WiseLord/ampcontrol-f103/src/tuner/tuner.c

#include "tuner.h"

#include <string.h>

#include "rds/parser.h"
#include "settings.h"
#include "stations.h"

#ifdef _RDA580X
#include "rda580x.h"
#endif
#ifdef _SI470X
#include "si470x.h"
#endif
#ifdef _TEA5767
#include "tea5767.h"
#endif
#ifdef _LC7213X
#include "lc7213x.h"
#endif

static Tuner tuner;

void tunerTestInit(TunerParam *tPar, TunerStatus *status)
{
    switch (tPar->band) {
    case TUNER_BAND_FM_JAPAN:
        tPar->fMin = 7600;
        tPar->fMax = 9100;
        break;
    case TUNER_BAND_FM_WORLDWIDE:
        tPar->fMin = 7600;
        tPar->fMax = 10800;
        break;
    case TUNER_BAND_FM_EASTEUROPE:
        tPar->fMin = 6500;
        tPar->fMax = 7600;
        break;
    default:
        tPar->fMin = 8700;
        tPar->fMax = 10800;
        break;
    }

    switch (tPar->step) {
    case TUNER_STEP_50K:
        tPar->fStep = 5;
        break;
    case TUNER_STEP_200K:
        tPar->fStep = 20;
        break;
    default:
        tPar->fStep = 10;
        break;
    }

    status->rssi = 10;
    status->flags = TUNER_STATUS_STEREO;
}

void tunerTestSetFreq(uint16_t value)
{
    tuner.status.freq = value;
}

static const TunerApi tunerTestApi = {
    .init = tunerTestInit,
    .setFreq = tunerTestSetFreq,
    .seek = tunerStep,
};


void tunerReadSettings(TunerIC defIC)
{
    stationsInit();

    // Read stored parameters
    memset(&tuner, 0, sizeof(tuner));

    tuner.par.ic = settingsRead(PARAM_TUNER_IC, defIC);
    tuner.par.band = settingsRead(PARAM_TUNER_BAND, TUNER_BAND_FM_US_EUROPE);
    tuner.par.step = settingsRead(PARAM_TUNER_STEP, TUNER_STEP_100K);
    tuner.par.deemph = settingsRead(PARAM_TUNER_DEEMPH, TUNER_DEEMPH_50u);

    tuner.par.volume = settingsRead(PARAM_TUNER_VOLUME, TUNER_VOLUME_MAX);
    tuner.status.freq = settingsRead(PARAM_TUNER_FREQ, 9950);
    tuner.par.flags = settingsRead(PARAM_TUNER_FLAGS, TUNER_PARAM_RDS);

    stationFavInit();

    // API initialization
    switch (tuner.par.ic) {
#ifdef _RDA580X
    case TUNER_IC_RDA5807:
        tuner.api = rda580xGetApi();
        break;
#endif
#ifdef _SI470X
    case TUNER_IC_SI4703:
        tuner.api = si470xGetApi();
        break;
#endif
#ifdef _TEA5767
    case TUNER_IC_TEA5767:
        tuner.api = tea5767GetApi();
        break;
#endif
#ifdef _LC7213X
    case TUNER_IC_LC7213X:
        tuner.api = lc7213xGetApi();
        break;
#endif
    case TUNER_IC_TEST:
        tuner.api = &tunerTestApi;
        break;
    default:
        tuner.api = NULL;
        break;
    }
}

void tunerSaveSettings(void)
{
    settingsStore(PARAM_TUNER_FREQ, (int16_t)tuner.status.freq);
    settingsStore(PARAM_TUNER_FLAGS, tuner.par.flags & ~TUNER_PARAM_MUTE);
}

void tunerInit(void)
{
    rdsParserReset();

    if (tuner.api && tuner.api->init) {
        tuner.api->init(&tuner.par, &tuner.status);
    }
}

Tuner *tunerGet(void)
{
    return &tuner;
}

void tunerSetPower(bool value)
{
    rdsParserReset();

    if (!value) {
        tunerSaveSettings();
    }

    if (tuner.api && tuner.api->setPower) {
        tuner.api->setPower(value);
    }
}

void tunerSetFreq(uint16_t value)
{
    rdsParserReset();

    const uint16_t freqMin = tuner.par.fMin;
    const uint16_t freqMax = tuner.par.fMax;

    if (value < freqMin) {
        value = freqMin;
    } else if (value > freqMax) {
        value = freqMax;
    }

    if (tuner.api && tuner.api->setFreq) {
        tuner.status.freq = value;
        tuner.api->setFreq(value);
    }
}

void tunerSetMute(bool value)
{
    if (value) {
        tuner.par.flags |= TUNER_PARAM_MUTE;
    } else {
        tuner.par.flags &= ~TUNER_PARAM_MUTE;
    }

    if (tuner.api && tuner.api->setMute) {
        tuner.api->setMute(value);
    }
}

void tunerSetBassBoost(bool value)
{
    if (value) {
        tuner.par.flags |= TUNER_PARAM_BASS;
    } else {
        tuner.par.flags &= ~TUNER_PARAM_BASS;
    }

    if (tuner.api && tuner.api->setBassBoost) {
        tuner.api->setBassBoost(value);
    }
}

void tunerSetForcedMono(bool value)
{
    if (value) {
        tuner.par.flags |= TUNER_PARAM_MONO;
    } else {
        tuner.par.flags &= ~TUNER_PARAM_MONO;
    }

    if (tuner.api && tuner.api->setForcedMono) {
        tuner.api->setForcedMono(value);
    }
}

void tunerSetRds(bool value)
{
    rdsParserReset();

    if (value) {
        tuner.par.flags |= TUNER_PARAM_RDS;
    } else {
        tuner.par.flags &= ~TUNER_PARAM_RDS;
    }

    if (tuner.api && tuner.api->setRds) {
        tuner.api->setRds(value);
    }
}

void tunerSetVolume(int8_t value)
{
    tuner.par.volume = value;

    if (tuner.api && tuner.api->setVolume) {
        tuner.api->setVolume(value);
    }
}

void tunerSeek(int8_t direction)
{
    rdsParserReset();

    if (tuner.api && tuner.api->seek) {
        tuner.api->seek(direction);
    }
}

void tunerStep(int8_t direction)
{
    uint16_t freq = tuner.status.freq;
    const uint16_t fMin = tuner.par.fMin;
    const uint16_t fMax = tuner.par.fMax;

    if (direction > 0) {
        if (freq == fMax) {
            freq = fMin;
        } else {
            freq += tuner.par.fStep;
        }
    } else {
        if (freq == fMin) {
            freq = fMax;
        } else {
            freq -= tuner.par.fStep;
        }
    }

    tunerSetFreq(freq);
}

void tunerMove(int8_t direction)
{
    if (tuner.par.flags & TUNER_PARAM_STA_MODE) {
        if (stationGetCount() > 0) {
            stationSeek(direction);
        } else {
            tunerStep(direction);
        }
    } else {
        tunerStep(direction);
    }
}

void tunerUpdateStatus(void)
{
    tuner.status.flags = TUNER_STATUS_INIT;

    if (tuner.api && tuner.api->updateStatus) {
        tuner.api->updateStatus();
    }
}
