WiseLord/ampcontrol-f103/src/tr/labels_en.c

#include "labels.h"

const char *const labels_en[LABEL_END] = {
    [LABEL_SUNDAY]          = "SUNDAY",
    [LABEL_MONDAY]          = "MONDAY",
    [LABEL_TUESDAY]         = "TUESDAY",
    [LABEL_WEDNESDAY]       = "WEDNESDAY",
    [LABEL_THURSDAY]        = "THURSDAY",
    [LABEL_FRIDAY]          = "FRIDAY",
    [LABEL_SATURDAY]        = "SATURDAY",

    [LABEL_VOLUME]          = "Volume",
    [LABEL_BASS]            = "Bass",
    [LABEL_MIDDLE]          = "Middle",
    [LABEL_TREBLE]          = "Treble",
    [LABEL_BALANCE]         = "Balance",
    [LABEL_FRONTREAR]       = "Front/rear",
    [LABEL_CENTER]          = "Center",
    [LABEL_SUBWOOFER]       = "Subwoofer",
    [LABEL_PREAMP]          = "Preamp",
    [LABEL_LOUDNESS]        = "Loudness",

    [LABEL_BASS_FREQ]       = "Bass freq",
    [LABEL_BASS_QUAL]       = "Bass Q",
    [LABEL_MIDDLE_KFREQ]    = "Middle freq",
    [LABEL_MIDDLE_QUAL]     = "Middle Q",
    [LABEL_TREBLE_KFREQ]    = "Treble freq",
    [LABEL_SUB_CUT_FREQ]    = "Sub cut freq",
    [LABEL_LOUD_PEAK_FREQ]  = "Loudness freq",

    [LABEL_IN_TUNER]        = "Tuner",
    [LABEL_IN_PC]           = "Computer",
    [LABEL_IN_AUX]          = "AUX",
    [LABEL_IN_BLUETOOTH]    = "Bluetooth",
    [LABEL_IN_KARADIO]      = "KaRadio",
    [LABEL_IN_USB]          = "USB",
    [LABEL_IN_SDCARD]       = "SD card",
    [LABEL_IN_MPD]          = "MPD",

    [LABEL_BOOL_OFF]        = "OFF",
    [LABEL_BOOL_ON]         = "ON",

    [LABEL_DB]              = "dB",
    [LABEL_HZ]              = "Hz",
    [LABEL_K]               = "k",

    [LABEL_IN_WAIT]         = "Waiting for",

    [LABEL_TUNER_FM_STATION_NAME]   = "FM station name",

    FOREACH_TUNER_IC(GENERATE_TUNER_IC_TEXT)

    [LABEL_TUNER_BAND + TUNER_BAND_FM_US_EUROPE]    = "US/Europe FM",
    [LABEL_TUNER_BAND + TUNER_BAND_FM_JAPAN]        = "Japan FM",
    [LABEL_TUNER_BAND + TUNER_BAND_FM_WORLDWIDE]    = "Worldwide FM",
    [LABEL_TUNER_BAND + TUNER_BAND_FM_EASTEUROPE]   = "East Europe FM",

    [LABEL_TUNER_STEP + TUNER_STEP_50K]     = "50kHz",
    [LABEL_TUNER_STEP + TUNER_STEP_100K]    = "100kHz",
    [LABEL_TUNER_STEP + TUNER_STEP_200K]    = "200kHz",

    [LABEL_TUNER_DEEMPH + TUNER_DEEMPH_50u] = "50us",
    [LABEL_TUNER_DEEMPH + TUNER_DEEMPH_75u] = "75us",

    [LABEL_SPECTRUM_MODE + SP_MODE_STEREO]      = "Stereo",
    [LABEL_SPECTRUM_MODE + SP_MODE_MIRROR]      = "Mirror",
    [LABEL_SPECTRUM_MODE + SP_MODE_INVERTED]    = "Inverted",
    [LABEL_SPECTRUM_MODE + SP_MODE_ANTIMIRROR]  = "Antimirror",
    [LABEL_SPECTRUM_MODE + SP_MODE_MIXED]       = "Mixed",

    [LABEL_PAL_MODE + PAL_SNOW]         = "Snow",
    [LABEL_PAL_MODE + PAL_AQUA]         = "Aqua",
    [LABEL_PAL_MODE + PAL_FIRE]         = "Fire",

    FOREACH_AUDIO_IC(GENERATE_AUDIO_IC_TEXT)

    [LABEL_AUDIO_MODE + AUDIO_MODE_2_0]     = "2.0",
    [LABEL_AUDIO_MODE + AUDIO_MODE_2_1]     = "2.1",
    [LABEL_AUDIO_MODE + AUDIO_MODE_4_0]     = "4.0",
    [LABEL_AUDIO_MODE + AUDIO_MODE_4_1]     = "4.1",
    [LABEL_AUDIO_MODE + AUDIO_MODE_5_1]     = "5.1",

    [LABEL_ALARM_DAY + ALARM_DAY_OFF]       = "Disabled",
    [LABEL_ALARM_DAY + ALARM_DAY_WEEKDAYS]  = "Weekdays",
    [LABEL_ALARM_DAY + ALARM_DAY_ALL_DAYS]  = "All days",

    // NOTE: Keep in sync with MenuIdx in menu.h
    [LABEL_MENU + MENU_NULL]            = "Up menu",

    [LABEL_MENU + MENU_SETUP]           = "Settings",

    [LABEL_MENU + MENU_SETUP_SYSTEM]    = "System",
    [LABEL_MENU + MENU_SETUP_AUDIO]     = "Audio",
    [LABEL_MENU + MENU_SETUP_TUNER]     = "Tuner",
    [LABEL_MENU + MENU_SETUP_SPECTRUM]  = "Spectrum",
    [LABEL_MENU + MENU_SETUP_DISPLAY]   = "Display",
    [LABEL_MENU + MENU_SETUP_ALARM]     = "Alarm",
    [LABEL_MENU + MENU_SETUP_RC]        = "Remote",

    [LABEL_MENU + MENU_SYSTEM_LANG]     = "Language",
    [LABEL_MENU + MENU_SYSTEM_I2C_EXT]  = "I2C expander",
    [LABEL_MENU + MENU_SYSTEM_ENC_RES]  = "Encoder resolution",
    [LABEL_MENU + MENU_SYSTEM_SIL_TIM]  = "Silence timer",
    [LABEL_MENU + MENU_SYSTEM_RTC_CORR] = "Time correction",
    [LABEL_MENU + MENU_SYSTEM_STBY_LOW] = "STBY active 0",
    [LABEL_MENU + MENU_SYSTEM_MUTE_LOW] = "MUTE active 0",

    [LABEL_MENU + MENU_I2C_EXT_IN_STAT] = "Input status",
    [LABEL_MENU + MENU_I2C_EXT_GPIO]    = "GPIO control",

    [LABEL_MENU + MENU_AUDIO_IC]        = "Audioproc",
    [LABEL_MENU + MENU_AUDIO_SHOWDB]    = "Show in dB",
    [LABEL_MENU + MENU_AUDIO_MODE]      = "Audio mode",
    [LABEL_MENU + MENU_AUDIO_IN]        = "Input",

    [LABEL_MENU + MENU_TUNER_IC]        = "Tuner IC",
    [LABEL_MENU + MENU_TUNER_BAND]      = "Band",
    [LABEL_MENU + MENU_TUNER_STEP]      = "Scan step",
    [LABEL_MENU + MENU_TUNER_DEEMPH]    = "Deemphasys",
    [LABEL_MENU + MENU_TUNER_STA_MODE]  = "Stations mode",
    [LABEL_MENU + MENU_TUNER_FMONO]     = "Force mono",
    [LABEL_MENU + MENU_TUNER_RDS]       = "Enable RDS",
    [LABEL_MENU + MENU_TUNER_BASS]      = "Bass boost",
    [LABEL_MENU + MENU_TUNER_VOLUME]    = "Volume",

    [LABEL_MENU + MENU_ALARM_HOUR]      = "Hour",
    [LABEL_MENU + MENU_ALARM_MINUTE]    = "Minute",
    [LABEL_MENU + MENU_ALARM_DAYS]      = "Days",

    [LABEL_MENU + MENU_SPECTRUM_MODE]   = "Display mode",
    [LABEL_MENU + MENU_SPECTRUM_PEAKS]  = "Peak level",
    [LABEL_MENU + MENU_SPECTRUM_GRAD]   = "Gradient",

    [LABEL_MENU + MENU_DISPLAY_BR_STBY] = "STBY brightness",
    [LABEL_MENU + MENU_DISPLAY_BR_WORK] = "Brightness",
    [LABEL_MENU + MENU_DISPLAY_ROTATE]  = "Rotate",
    [LABEL_MENU + MENU_DISPLAY_DEF]     = "Main screen",
    [LABEL_MENU + MENU_DISPLAY_PALETTE] = "Palette",
    [LABEL_MENU + MENU_DISPLAY_SCRSAVER] = "Screensaver",

    // NOTE: Keep in sync with cmd.h define list
    [LABEL_MENU + MENU_RC_STBY_SWITCH]  = "Switch standby",
    [LABEL_MENU + MENU_RC_MUTE]         = "Mute",
    [LABEL_MENU + MENU_RC_VOL_UP]       = "Volume up",
    [LABEL_MENU + MENU_RC_VOL_DOWN]     = "Volume down",
    [LABEL_MENU + MENU_RC_MENU]         = "Menu",
    [LABEL_MENU + MENU_RC_CHAN_NEXT]    = "Next chan",
    [LABEL_MENU + MENU_RC_CHAN_PREV]    = "Prev chan",
    [LABEL_MENU + MENU_RC_DIG]          = "Digit",
    [LABEL_MENU + MENU_RC_IN_NEXT]      = "Next input",
    [LABEL_MENU + MENU_RC_NAV_OK]       = "OK",
    [LABEL_MENU + MENU_RC_NAV_BACK]     = "Back",
    [LABEL_MENU + MENU_RC_NAV_RIGHT]    = "Right",
    [LABEL_MENU + MENU_RC_NAV_UP]       = "Up",
    [LABEL_MENU + MENU_RC_NAV_LEFT]     = "Left",
    [LABEL_MENU + MENU_RC_NAV_DOWN]     = "Down",
    [LABEL_MENU + MENU_RC_BASS_UP]      = "Bass up",
    [LABEL_MENU + MENU_RC_BASS_DOWN]    = "Bass down",
    [LABEL_MENU + MENU_RC_MIDDLE_UP]    = "Middle up",
    [LABEL_MENU + MENU_RC_MIDDLE_DOWN]  = "Middle down",
    [LABEL_MENU + MENU_RC_TREBLE_UP]    = "Treble up",
    [LABEL_MENU + MENU_RC_TREBLE_DOWN]  = "Treble down",
    [LABEL_MENU + MENU_RC_LOUDNESS]     = "Loudness",
    [LABEL_MENU + MENU_RC_SURROUND]     = "Surround",
    [LABEL_MENU + MENU_RC_EFFECT_3D]    = "3D-effect",
    [LABEL_MENU + MENU_RC_TONE_BYPASS]  = "Bypass tone",
    [LABEL_MENU + MENU_RC_TIME]         = "Time",
    [LABEL_MENU + MENU_RC_STOP]         = "Stop",
    [LABEL_MENU + MENU_RC_PLAY_PAUSE]   = "Play/pause",
    [LABEL_MENU + MENU_RC_REW]          = "Rewind",
    [LABEL_MENU + MENU_RC_FWD]          = "Flash forward",
    [LABEL_MENU + MENU_RC_TIMER]        = "Timer",
    [LABEL_MENU + MENU_RC_SP_MODE]      = "Spectrum mode",
    [LABEL_MENU + MENU_RC_SCR_DEF]      = "Default screen",
    [LABEL_MENU + MENU_RC_BT_IN_NEXT]   = "Next BT input",
    [LABEL_MENU + MENU_RC_TUNER_MONO]   = "Tuner mono",
    [LABEL_MENU + MENU_RC_REPEAT]       = "Repeat",
    [LABEL_MENU + MENU_RC_RANDOM]       = "Random",
};
