WiseLord/ampcontrol-f103/src/tr/labels_tr.c

#include "labels.h"

const char *const labels_tr[LABEL_END] = {
    [LABEL_SUNDAY]          = "Pazar",
    [LABEL_MONDAY]          = "Pazartesi",
    [LABEL_TUESDAY]         = "Salı",
    [LABEL_WEDNESDAY]       = "Çarşamba",
    [LABEL_THURSDAY]        = "Perşembe",
    [LABEL_FRIDAY]          = "Cuma",
    [LABEL_SATURDAY]        = "Cumartesi",

    [LABEL_VOLUME]          = "Volum",
    [LABEL_BASS]            = "Bass",
    [LABEL_MIDDLE]          = "Orta Ses",
    [LABEL_TREBLE]          = "Tiz",
    [LABEL_BALANCE]         = "Sağ/Sol Denge",
    [LABEL_FRONTREAR]       = "Ön/Arka Denge",
    [LABEL_CENTER]          = "Merkez",
    [LABEL_SUBWOOFER]       = "Subwoofer",
    [LABEL_PREAMP]          = "Kazanç",

    [LABEL_IN_TUNER]        = "Radio",
    [LABEL_IN_PC]           = "Bilgisayar",
    //    [LABEL_IN_AUX]          = "AUX",
    //    [LABEL_IN_BLUETOOTH]    = "Bluetooth",
    //    [LABEL_IN_KARADIO]      = "KaRadio",
    //    [LABEL_IN_USB]          = "USB",
    [LABEL_IN_SDCARD]       = "SD Kart",
//    [LABEL_IN_MPD]          = "MPD",

    [LABEL_BOOL_OFF]        = "Kapalı",
    [LABEL_BOOL_ON]         = "Açık",

//    [LABEL_IN_WAIT]         = "Wait for",

    [LABEL_TUNER_FM_STATION_NAME]   = "FM Radyo İsimleri:",

    [LABEL_TUNER_IC + TUNER_IC_NO]      = "Yok",

    [LABEL_TUNER_BAND + TUNER_BAND_FM_US_EUROPE]    = "ABD/Avrupa FM",
    [LABEL_TUNER_BAND + TUNER_BAND_FM_JAPAN]        = "Japan FM",
    [LABEL_TUNER_BAND + TUNER_BAND_FM_WORLDWIDE]    = "Dünya Çapında FM",
    [LABEL_TUNER_BAND + TUNER_BAND_FM_EASTEUROPE]   = "Doğu Avrupa FM",

    [LABEL_TUNER_STEP + TUNER_STEP_50K]     = "50kHz",
    [LABEL_TUNER_STEP + TUNER_STEP_100K]    = "100kHz",
    [LABEL_TUNER_STEP + TUNER_STEP_200K]    = "200kHz",

    [LABEL_TUNER_DEEMPH + TUNER_DEEMPH_50u] = "50us",
    [LABEL_TUNER_DEEMPH + TUNER_DEEMPH_75u] = "75us",

    [LABEL_SPECTRUM_MODE + SP_MODE_STEREO]      = "Stereo",
//    [LABEL_SPECTRUM_MODE + SP_MODE_MIRROR]      = "Mirror",
//    [LABEL_SPECTRUM_MODE + SP_MODE_INVERTED]    = "Inverted",
//    [LABEL_SPECTRUM_MODE + SP_MODE_ANTIMIRROR]  = "Antimirror",
    [LABEL_SPECTRUM_MODE + SP_MODE_MIXED]       = "Karışık",

    [LABEL_PAL_MODE + PAL_SNOW]         = "Kar Teması",
    [LABEL_PAL_MODE + PAL_AQUA]         = "Su Teması",
    [LABEL_PAL_MODE + PAL_FIRE]         = "Ateş Teması",

    [LABEL_AUDIO_IC + AUDIO_IC_NO]      = "Yok",

    [LABEL_ALARM_DAY + ALARM_DAY_OFF]       = "Kapalı",
    [LABEL_ALARM_DAY + ALARM_DAY_WEEKDAYS]  = "Hafta İçi",
    [LABEL_ALARM_DAY + ALARM_DAY_ALL_DAYS]  = "Tüm Günler",

    // NOTE: Keep in sync with MenuIdx in menu.h
    [LABEL_MENU + MENU_NULL]            = "Bir Önceki Menü'ye Dön",

    [LABEL_MENU + MENU_SETUP]           = "Menü Ayarları",

    [LABEL_MENU + MENU_SETUP_SYSTEM]    = "Sistem Ayarı",
    [LABEL_MENU + MENU_SETUP_AUDIO]     = "Ses İşlemci Ayarı",
    [LABEL_MENU + MENU_SETUP_TUNER]     = "Radyo İşlemci Ayarı",
    [LABEL_MENU + MENU_SETUP_SPECTRUM]  = "Spectrum Ayarı",
    [LABEL_MENU + MENU_SETUP_DISPLAY]   = "Ekran Ayarı",
    [LABEL_MENU + MENU_SETUP_ALARM]     = "Alarm Ayarı",
    [LABEL_MENU + MENU_SETUP_RC]        = "Kumanda Ayarı",

    [LABEL_MENU + MENU_SYSTEM_LANG]     = "Dil Seçeneği",
    [LABEL_MENU + MENU_SYSTEM_I2C_EXT]  = "I2C Genişletici",
    [LABEL_MENU + MENU_SYSTEM_ENC_RES]  = "Enkoder Çözünürlüğü",
    [LABEL_MENU + MENU_SYSTEM_SIL_TIM]  = "Sessizlik Zamanlayıcısı",
    [LABEL_MENU + MENU_SYSTEM_RTC_CORR] = "Zaman Düzeltme",
//    [LABEL_MENU + MENU_SYSTEM_STBY_LOW] = "STBY active 0",
//    [LABEL_MENU + MENU_SYSTEM_MUTE_LOW] = "MUTE active 0",

    [LABEL_MENU + MENU_I2C_EXT_IN_STAT] = "Giriş Durumu",
    [LABEL_MENU + MENU_I2C_EXT_GPIO]    = "GPIO Kontrolü",

    [LABEL_MENU + MENU_AUDIO_IC]        = "Ses İşlemci Modeli",
//    [LABEL_MENU + MENU_AUDIO_SHOWDB]    = "Show in dB",
//    [LABEL_MENU + MENU_AUDIO_MODE]      = "Audio mode",
    [LABEL_MENU + MENU_AUDIO_IN]        = "Ses Giriş",

    [LABEL_MENU + MENU_TUNER_IC]        = "Tuner İşlemci Modeli",
    [LABEL_MENU + MENU_TUNER_BAND]      = "Bant Modeli",
    [LABEL_MENU + MENU_TUNER_STEP]      = "Tarama Adımı",
    [LABEL_MENU + MENU_TUNER_DEEMPH]    = "Vurgulama",
    [LABEL_MENU + MENU_TUNER_STA_MODE]  = "Kontrol modu",
    [LABEL_MENU + MENU_TUNER_FMONO]     = "Mono Ses",
    [LABEL_MENU + MENU_TUNER_RDS]       = "Rds Bilgi Gösterimi",
    [LABEL_MENU + MENU_TUNER_BASS]      = "Bass Kuvetlendirme",
    [LABEL_MENU + MENU_TUNER_VOLUME]    = "Tuner Ses Ayarı",

    [LABEL_MENU + MENU_ALARM_HOUR]      = "Saat",
    [LABEL_MENU + MENU_ALARM_MINUTE]    = "Dakika",
    [LABEL_MENU + MENU_ALARM_DAYS]      = "Günler",

    [LABEL_MENU + MENU_SPECTRUM_MODE]   = "Spectrum Tipi",
    [LABEL_MENU + MENU_SPECTRUM_PEAKS]  = "Tepe Seviyesi",
    [LABEL_MENU + MENU_SPECTRUM_GRAD]   = "Eğim",

    [LABEL_MENU + MENU_DISPLAY_BR_STBY] = "Bekleme Parlaklığı",
    [LABEL_MENU + MENU_DISPLAY_BR_WORK] = "Genel Parlaklık",
    [LABEL_MENU + MENU_DISPLAY_ROTATE]  = "Ekran Döndürme",
    [LABEL_MENU + MENU_DISPLAY_DEF]     = "Ana Ekran",
    [LABEL_MENU + MENU_DISPLAY_PALETTE] = "Tema Renkleri",
//    [LABEL_MENU + MENU_DISPLAY_SCRSAVER] = "Screensaver",

    // NOTE: Keep in sync with cmd.h define list
    [LABEL_MENU + MENU_RC_STBY_SWITCH]  = "Bekleme Butonu",
    [LABEL_MENU + MENU_RC_MUTE]         = "Mute",
    [LABEL_MENU + MENU_RC_VOL_UP]       = "Volum Artı",
    [LABEL_MENU + MENU_RC_VOL_DOWN]     = "Volum Eksi",
    [LABEL_MENU + MENU_RC_MENU]         = "Menü",
    [LABEL_MENU + MENU_RC_CHAN_NEXT]    = "Sornaki Kanal",
    [LABEL_MENU + MENU_RC_CHAN_PREV]    = "Önceki Kanal",
    [LABEL_MENU + MENU_RC_DIG]          = "Buton",
    [LABEL_MENU + MENU_RC_IN_NEXT]      = "Sonraki Giriş",
    [LABEL_MENU + MENU_RC_NAV_OK]       = "Tamam",
    [LABEL_MENU + MENU_RC_NAV_BACK]     = "Geri",
    [LABEL_MENU + MENU_RC_NAV_RIGHT]    = "Sağ",
    [LABEL_MENU + MENU_RC_NAV_UP]       = "Yukarı",
    [LABEL_MENU + MENU_RC_NAV_LEFT]     = "Sol",
    [LABEL_MENU + MENU_RC_NAV_DOWN]     = "Aşağı",
    [LABEL_MENU + MENU_RC_BASS_UP]      = "Bass Artı",
    [LABEL_MENU + MENU_RC_BASS_DOWN]    = "Bass Eksi",
    [LABEL_MENU + MENU_RC_MIDDLE_UP]    = "Orta Ses Artı",
    [LABEL_MENU + MENU_RC_MIDDLE_DOWN]  = "Orta Ses Eksi",
    [LABEL_MENU + MENU_RC_TREBLE_UP]    = "Tiz Artı",
    [LABEL_MENU + MENU_RC_TREBLE_DOWN]  = "Tiz Eksi",
    [LABEL_MENU + MENU_RC_LOUDNESS]     = "Ses Yükseltme",
    [LABEL_MENU + MENU_RC_SURROUND]     = "Kuşatma",
    [LABEL_MENU + MENU_RC_EFFECT_3D]    = "3D-Efekt",
    [LABEL_MENU + MENU_RC_TONE_BYPASS]  = "Ton Baypas",
    [LABEL_MENU + MENU_RC_TIME]         = "Saat Ayarı",
    [LABEL_MENU + MENU_RC_STOP]         = "Durdur",
    [LABEL_MENU + MENU_RC_PLAY_PAUSE]   = "Oynat/Duraklat",
    [LABEL_MENU + MENU_RC_REW]          = "Geri Sar",
    [LABEL_MENU + MENU_RC_FWD]          = "İleri Sar",
    [LABEL_MENU + MENU_RC_TIMER]        = "Kapatma Saati",
    [LABEL_MENU + MENU_RC_SP_MODE]      = "Spektrum modu",
    [LABEL_MENU + MENU_RC_SCR_DEF]      = "Varsayılan ekran",
    [LABEL_MENU + MENU_RC_BT_IN_NEXT]   = "Sonraki BT Giriş",
//    [LABEL_MENU + MENU_RC_TUNER_MONO]   = "Tuner mono",
//    [LABEL_MENU + MENU_RC_REPEAT]       = "Repeat",
//    [LABEL_MENU + MENU_RC_RANDOM]       = "Random",
};
