WiseLord/ampcontrol-f103/src/tuner/rda580x_regs.h

#ifndef RDA580X_REGS_H
#define RDA580X_REGS_H

#ifdef __cplusplus
extern "C" {
#endif

// Write mode

// 0 register (02H)
#define RDA580X_DHIZ                0x80 // Audio out enable (1) / High impedance (0)
#define RDA580X_DMUTE               0x40 // Audio unmuted (1) / muted (0)
#define RDA580X_MONO                0x20 // Mono mode (1) / stereo mode (0)
#define RDA5807_BASS                0x10 // Bass boost (1)
#define RDA580X_RCLK_NON_CAL_MODE   0x08 // RCLK always on (0)
#define RDA580X_RCLK_DIR_IN_MODE    0x04 // RCLK direct input mode (1)
#define RDA580X_SEEKUP              0x02 // Seek up (1) / down (0)
#define RDA580X_SEEK                0x01 // Stop seek (0) / start seek in SEEKUP direction (1)

// 1 register (02L)
#define RDA580X_SKMODE              0x80 // Stop seeking on band limit (1)
#define RDA580X_CLK_MODE            0x70 // Select clock mode
#define RDA580X_CLK_MODE_32768      0x00 // Select quartz frequency
#define RDA580X_CLK_MODE_12M        0x10
#define RDA580X_CLK_MODE_24M        0x50
#define RDA580X_CLK_MODE_13M        0x20
#define RDA580X_CLK_MODE_26M        0x60
#define RDA580X_CLK_MODE_19M2       0x30
#define RDA580X_CLK_MODE_38M4       0x70
#define RDA5807_RDS_EN              0x08 // RDS/RBDS enable (1)
#define RDA5807_NEW_METHOD          0x04 // New demodulation method (1)
#define RDA580X_SOFT_RESET          0x02 // Reset settings (1)
#define RDA580X_ENABLE              0x01 // Power on radio (1)

// 2 register (03H)
#define RDA580X_CHAN_9_2            0xFF // CHAN 9..2 bits

// 3 register (03L)
// CHAN 1.. 0 bits
#define RDA580X_CHAN_1_0            0xC0 // CHAN 1..0 bits
#define RDA5807_DIRECT_MODE         0x20 // Direct mode (1), only used when test
#define RDA580X_TUNE                0x10 // Tune enable (1)
#define RDA580X_BAND                0x0C // Tuner band selection
#define RDA580X_BAND_US_EUROPE      0x00 // 87..108 MHz
#define RDA580X_BAND_JAPAN          0x04 // 76..91 MHz
#define RDA580X_BAND_WORLDWIDE      0x08 // 76..108 MHz
#define RDA580X_BAND_EASTEUROPE     0x0C // 65..76 MHz
#define RDA580X_SPACE               0x03 // Channel spacing
#define RDA580X_SPACE_100           0x00 // 100kHz step
#define RDA580X_SPACE_200           0x01 // 200kHz step
#define RDA580X_SPACE_50            0x02 // 50kHz step
#define RDA580X_SPACE_25            0x03 // 25kHz step

// 4 register (04H)
#define RDA580X_STCIEN              0x40 // Enable low pulse on GPIO2 when interrupt occurs (1)
#define RDA580X_DE                  0x08 // De-emphasis 75us (0) / 50us (1)
#define RDA580X_SOFTMUTE_EN         0x02 // Softmute enable (1)
#define RDA580X_AFCD                0x01 // AFC disable (1)

// 5 register (04L)
#define RDA580X_I2S_ENABLED         0x40 // I2S bus enable (1)
#define RDA580X_GPIO3               0x30 // GPIO3 control
#define RDA580X_GPIO3_HI_IMP        0x00 // GPIO3 high impedance
#define RDA580X_GPIO3_ST_IND        0x10 // GPIO3 as stereo indicator
#define RDA580X_GPIO3_LO            0x20 // GPIO3 low level
#define RDA580X_GPIO3_HI            0x30 // GPIO3 high level
#define RDA580X_GPIO2               0x0C // GPIO2 control
#define RDA580X_GPIO2_HI_IMP        0x00 // GPIO2 high impedance
#define RDA580X_GPIO2_INT           0x04 // GPIO2 interrupt (INT)
#define RDA580X_GPIO2_LO            0x08 // GPIO2 low level
#define RDA580X_GPIO2_HI            0x0C // GPIO2 high level
#define RDA580X_GPIO1               0x0C // GPIO1 control
#define RDA580X_GPIO1_HI_IMP        0x00 // GPIO1 high impedance
#define RDA580X_GPIO1_RSRVD         0x04 // GPIO1 reserved
#define RDA580X_GPIO1_LO            0x08 // GPIO1 low level
#define RDA580X_GPIO1_HI            0x0C // GPIO1 high level

// 6 register (05H)
#define RDA5807_INT_MODE            0x80 // 5ms interrupt for RDSIEN on RDS ready (0)
#define RDA5807_SEEKTH              0x0F // Seek SNR threshold, 4bits, default 1000=32dB

// 7 register (05L)
#define RDA5802_LNA_PORT_SEL        0xC0 // LNA input port selection bit
#define RDA5802_LNA_PORT_SEL_NO     0x00 // no input
#define RDA5802_LNA_PORT_SEL_LNAN   0x40 // LNAN
#define RDA580X_LNA_PORT_SEL_LNAP   0x80 // LNAP (FMIN on RDA5807_FP)
#define RDA5802_LNA_PORT_SEL_DUAL   0xC0 // Dual port input
#define RDA5802_LNA_ICSEL_BIT       0x30 // LNA working current bit
#define RDA5802_LNA_ICSEL_BIT_1_8   0x00 // 1.8mA
#define RDA5802_LNA_ICSEL_BIT_2_1   0x10 // 2.1mA
#define RDA5802_LNA_ICSEL_BIT_2_5   0x20 // 2.5mA
#define RDA5802_LNA_ICSEL_BIT_3_0   0x30 // 3.0mA
#define RDA580X_VOLUME              0x0F // 4 bits volume (0000 - muted, 1111 - max)

// 8 register (06H)
#define RDA5807_OPEN_MODE           0x60 // 2 bits (11) to open read-only regs for writing
#define RDA580X_I2S_MODE            0x10 // I2S master (0) or slave (1) mode
#define RDA5807_SW_LR               0x08 // WS relation to l/r channel: ws=0->r,ws=1->l (0) or ws=0->l,ws=1->r (1)
#define RDA5807_SCLK_I_EDGE         0x04 // Normal (0) or inverted (1) sclk
#define RDA5807_DATA_SIGNED         0x02 // Unsigned (0) or signed (1) 16-bit audio data
#define RDA5807_WL_I_EDGE           0x01 // Normal (0) or inverted (1) ws

// 9 register (06L)
#define RDA580X_I2S_WS_CNT          0xF0 // I2S WS_STEP selection in master mode
#define RDA580X_I2S_WS_CNT_48       0x80 // I2S WS_STEP=48 kpbs
#define RDA580X_I2S_WS_CNT_44_1     0x70 // I2S WS_STEP=44.1 kbps
#define RDA580X_I2S_WS_CNT_32       0x60 // I2S WS_STEP=32 kbps
#define RDA580X_I2S_WS_CNT_24       0x50 // I2S WS_STEP=24 kbps
#define RDA580X_I2S_WS_CNT_22_05    0x40 // I2S WS_STEP=22.05 kbps
#define RDA580X_I2S_WS_CNT_16       0x30 // I2S WS_STEP=16 kbps
#define RDA580X_I2S_WS_CNT_12       0x20 // I2S WS_STEP=12 kbps
#define RDA580X_I2S_WS_CNT_11_025   0x10 // I2S WS_STEP=11.025 kbps
#define RDA580X_I2S_WS_CNT_8        0x00 // I2S WS_STEP=8 kbps (default)
#define RDA5807_WS_O_EDGE           0x08 // Invert (1) ws output when as master
#define RDA5807_SCLK_O_EDGE         0x04 // Invert (1) sclk output when as master
#define RDA5807_L_DELY              0x02 // Left channel data delay 1T (1)
#define RDA5807_R_DELY              0x01 // Right channel data delay 1T (1)

// 10 register (07H)
#define RDA5807_TH_SOFRBLEND        0x7C // 5 bits for noise soft blend
#define RDA5807_TH_SOFRBLEND_DEF    0x40 // default 10000
#define RDA5807_65M_50M_MODE        0x02 // For BAND=11, 50..76MHz (0), default 1

// 11 register (07L)
#define RDA5807_SEEK_TH_OLD         0xFC // 6 bits seek treshold in old seek mode, valid for SKMODE=1
#define RDA5807_SEEK_TH_OLD_DEF     0x80 // default
#define RDA5807_SOFTBLEND_EN        0x02 // Softblend enable (1)
#define RDA5807_FREQ_MODE           0x01 // Manual freq setup (1) for 12,13 regs

// 12 register (08H)
#define RDA5807_DIRECT_FREQ_HI      0xFF // High byte of direct freq offset

// 13 register (08L)
#define RDA5807_DIRECT_FREQ_LO      0xFF // High byte of direct freq offset

// Read mode

// 0 register (0AH)
#define RDA5807_RDSR                0x80 // RDS ready (1)
#define RDA580X_STC                 0x40 // Seek/tune complete (1)
#define RDA580X_SF                  0x20 // Seek failure (1)
#define RDA5807_RDSS                0x10 // RDS synchronized (1)
#define RDA5807_BLK_E               0x08 // (When RDS enabled) block E has been found (1)
#define RDA580X_ST                  0x04 // Stereo indicator (1)
#define RDA580X_READCHAN_9_8        0x03 // READCHAN 9..8 bits

// 1 register (0AL)
#define RDA580X_READCHAN_7_0        0xFF // READCHAN 7..0 bits

// 2 register (0BH)
#define RDA580X_RSSI                0xFE // 7 bits of RSSI signal level
#define RDA580X_FM_TRUE             0x01 // Current channel is a station (1)

// 3 register (0BL)
#define RDA580X_FM_READY            0x80 // Ready
#define RDA5807_ABCD_E              0x10 // Data block E (1) or blocks A-D (0)
#define RDA5807_BLERA               0x0C // 2 bits error level in block A(RDS) or E(RBDS)
#define RDA5807_BLERB               0x03 // 2 bits error level in block B(RDS) or E(RBDS)

// 4 register (0CH)
#define RDA5807_RDSA_HI             0xFF // RDS block A data high
// 5 register (0CL)
#define RDA5807_RDSA_LO             0xFF // RDS block A data low

// 6 register (0DH)
#define RDA5807_RDSB_HI             0xFF // RDS block B data high
// 7 register (0DL)
#define RDA5807_RDSB_LO             0xFF // RDS block B data low

// 8 register (0EH)
#define RDA5807_RDSC_HI             0xFF // RDS block C data high
// 9 register (0EL)
#define RDA5807_RDSC_LO             0xFF // RDS block C data low

// 10 register (0FH)
#define RDA5807_RDSD_HI             0xFF // RDS block D data high
// 11 register (0FL)
#define RDA5807_RDSD_LO             0xFF // RDS block D data low

#ifdef __cplusplus
}
#endif

#endif // RDA580X_REGS_H
