WiseLord/ampcontrol-f103/display/ili9341.c

#include "ili9341.h"

#include <stm32f1xx_ll_bus.h>
#include <stm32f1xx_ll_spi.h>

#include "../pins.h"
#include "../functions.h"

#include "gc320x240.h"

#define ILI9341_WIDTH           240
#define ILI9341_HEIGHT          320
#define ILI9341_PIXELS          (ILI9341_WIDTH * ILI9341_HEIGHT)

#define TX_BUSY()               (LL_SPI_IsActiveFlag_BSY(SPI1) || !LL_SPI_IsActiveFlag_TXE(SPI1))

static GlcdDriver glcd = {
    .clear = ili9341Clear,
    .drawPixel = ili9341DrawPixel,
    .drawRectangle = ili9341DrawRectangle,
    .drawImage = ili9341DrawImage,
};

static inline void ili9341SendSPI(uint8_t data) __attribute__((always_inline));
static inline void ili9341SendSPI(uint8_t data)
{
    while (!LL_SPI_IsActiveFlag_TXE(SPI1));
    LL_SPI_TransmitData8(SPI1, data);
}

static inline void ili9341SendCmd(uint8_t cmd) __attribute__((always_inline));
static inline void ili9341SendCmd(uint8_t cmd)
{
    while (TX_BUSY());
    CLR(ILI9341_DC);
    LL_SPI_TransmitData8(SPI1, cmd);
    while (TX_BUSY());
    SET(ILI9341_DC);
}

static inline void ili9341SendData(uint16_t data) __attribute__((always_inline));
static inline void ili9341SendData(uint16_t data)
{
    uint8_t dataH = data >> 8;
    uint8_t dataL = data & 0xFF;

    ili9341SendSPI(dataH);
    ili9341SendSPI(dataL);
}

static void ili9341InitSeq(void)
{
    _delay_ms(50);

    CLR(ILI9341_CS);

    ili9341SendCmd(ILI9341_SWRESET);
    _delay_ms(10);
    ili9341SendCmd(ILI9341_DISPOFF);

    ili9341SendCmd(ILI9341_PWCTRLB);
    ili9341SendSPI(0x00);
    ili9341SendSPI(0xC1);
    ili9341SendSPI(0x30);

    ili9341SendCmd(ILI9341_PWSEQCTL);
    ili9341SendSPI(0x64);
    ili9341SendSPI(0x03);
    ili9341SendSPI(0x12);
    ili9341SendSPI(0x81);

    ili9341SendCmd(ILI9341_DRVTIMCTLA1);
    ili9341SendSPI(0x85);
    ili9341SendSPI(0x01);
    ili9341SendSPI(0x79);

    ili9341SendCmd(ILI9341_PWCTRLA);
    ili9341SendSPI(0x39);
    ili9341SendSPI(0x2C);
    ili9341SendSPI(0x00);
    ili9341SendSPI(0x34);
    ili9341SendSPI(0x02);

    ili9341SendCmd(ILI9341_PUMPRTCTL);
    ili9341SendSPI(0x20);

    ili9341SendCmd(ILI9341_DRVTIMB);
    ili9341SendSPI(0x00);
    ili9341SendSPI(0x00);

    ili9341SendCmd(ILI9341_PWCTRL1);
    ili9341SendSPI(0x26);

    ili9341SendCmd(ILI9341_PWCTRL2);
    ili9341SendSPI(0x11);

    ili9341SendCmd(ILI9341_VMCTRL1);
    ili9341SendSPI(0x35);
    ili9341SendSPI(0x3E);

    ili9341SendCmd(ILI9341_VMCTRL2);
    ili9341SendSPI(0xBE);

    ili9341SendCmd(ILI9341_PIXSET);
    ili9341SendSPI(0x55);

    ili9341SendCmd(ILI9341_FRMCTR1);
    ili9341SendSPI(0x00);
    ili9341SendSPI(0x1B);

    ili9341SendCmd(ILI9341_EN3G);
    ili9341SendSPI(0x08);

    ili9341SendCmd(ILI9341_GAMSET);
    ili9341SendSPI(0x01);

    ili9341SendCmd(ILI9341_ETMOD);
    ili9341SendSPI(0x07);

    ili9341SendCmd(ILI9341_DISCTRL);
    ili9341SendSPI(0x08);
    ili9341SendSPI(0x82);
    ili9341SendSPI(0x27);

    // Retate
    ili9341SendCmd(ILI9341_MADCTL);
    ili9341SendSPI(0x08);

    ili9341SendCmd(ILI9341_PGAMCTRL);
    ili9341SendSPI(0x0F);
    ili9341SendSPI(0x31);
    ili9341SendSPI(0x2B);
    ili9341SendSPI(0x0C);
    ili9341SendSPI(0x0E);
    ili9341SendSPI(0x08);
    ili9341SendSPI(0x4E);
    ili9341SendSPI(0xF1);
    ili9341SendSPI(0x37);
    ili9341SendSPI(0x07);
    ili9341SendSPI(0x10);
    ili9341SendSPI(0x03);
    ili9341SendSPI(0x0E);
    ili9341SendSPI(0x09);
    ili9341SendSPI(0x00);

    ili9341SendCmd(ILI9341_NGAMCTRL);
    ili9341SendSPI(0x00);
    ili9341SendSPI(0x0E);
    ili9341SendSPI(0x14);
    ili9341SendSPI(0x03);
    ili9341SendSPI(0x11);
    ili9341SendSPI(0x07);
    ili9341SendSPI(0x31);
    ili9341SendSPI(0xC1);
    ili9341SendSPI(0x48);
    ili9341SendSPI(0x08);
    ili9341SendSPI(0x0F);
    ili9341SendSPI(0x0C);
    ili9341SendSPI(0x31);
    ili9341SendSPI(0x36);
    ili9341SendSPI(0x0F);

    ili9341SendCmd(ILI9341_SLPOUT);
    ili9341SendCmd(ILI9341_DISPON);

    while (TX_BUSY());
    SET(ILI9341_CS);
}

void ili9341SetWindow(uint16_t x, uint16_t y, uint16_t w, uint16_t h)
{
    ili9341SendCmd(ILI9341_PASET);
    ili9341SendData(x);
    ili9341SendData(x + w - 1);

    ili9341SendCmd(ILI9341_CASET);
    ili9341SendData(y);
    ili9341SendData(y + h - 1);

    ili9341SendCmd(ILI9341_RAMWR);
}

static void ili9341InitSPI()
{
    LL_APB2_GRP1_EnableClock(LL_APB2_GRP1_PERIPH_SPI1);

    LL_SPI_InitTypeDef SPI_InitStruct;
    SPI_InitStruct.Mode = LL_SPI_MODE_MASTER;
    SPI_InitStruct.TransferDirection = LL_SPI_FULL_DUPLEX;
    SPI_InitStruct.BaudRate = LL_SPI_BAUDRATEPRESCALER_DIV4;
    SPI_InitStruct.ClockPolarity = LL_SPI_POLARITY_LOW;
    SPI_InitStruct.ClockPhase = LL_SPI_PHASE_1EDGE;
    SPI_InitStruct.BitOrder = LL_SPI_MSB_FIRST;
    SPI_InitStruct.DataWidth = LL_SPI_DATAWIDTH_8BIT;
    SPI_InitStruct.NSS = LL_SPI_NSS_SOFT;
    SPI_InitStruct.CRCCalculation = LL_SPI_CRCCALCULATION_DISABLE;
    SPI_InitStruct.CRCPoly = 10;
    LL_SPI_Init(SPI1, &SPI_InitStruct);

    LL_SPI_Enable(SPI1);
}

void ili9341Init(GlcdDriver **driver)
{
    *driver = &glcd;
    gc320x240Init(*driver);

    // Configure Hardware SPI
    ili9341InitSPI();

    CLR(ILI9341_RST);
    _delay_ms(100);
    SET(ILI9341_RST);

    // Init magic
    ili9341InitSeq();
    SET(ILI9341_LED);
}

void ili9341Clear(void)
{
    ili9341DrawRectangle(0, 0, glcd.canvas->width, glcd.canvas->height, glcd.canvas->color);
}

void ili9341Sleep(void)
{
    CLR(ILI9341_CS);
    ili9341SendCmd(ILI9341_SLPIN);
    while (TX_BUSY());
    SET(ILI9341_CS);
}

void ili9341Wakeup(void)
{
    CLR(ILI9341_CS);
    ili9341SendCmd(ILI9341_SLPOUT);
    while (TX_BUSY());
    SET(ILI9341_CS);
}

void ili9341DrawPixel(int16_t x, int16_t y, uint16_t color)
{
    CLR(ILI9341_CS);
    ili9341SetWindow(x, y, 1, 1);
    ili9341SendData(color);
    while (TX_BUSY());
    SET(ILI9341_CS);
}

void ili9341DrawRectangle(uint16_t x, uint16_t y, uint16_t w, uint16_t h, uint16_t color)
{
    uint8_t colorH = color >> 8;
    uint8_t colorL = color & 0xFF;

    CLR(ILI9341_CS);

    ili9341SetWindow(x, y, w, h);

    for (uint16_t i = 0; i < w; i++) {
        for (uint16_t j = 0; j < h; j++) {
            ili9341SendSPI(colorH);
            ili9341SendSPI(colorL);
        }
    }

    while (TX_BUSY());
    SET(ILI9341_CS);
}

void ili9341DrawImage(tImage *img)
{
    uint16_t w = img->width;
    uint16_t h = img->height;
    uint16_t x0 = glcd.canvas->x;
    uint16_t y0 = glcd.canvas->y;
    uint8_t colorH = glcd.font.color >> 8;
    uint8_t colorL = glcd.font.color & 0xFF;
    uint8_t bgColorH = glcd.canvas->color >> 8;
    uint8_t bgColorL = glcd.canvas->color & 0xFF;
    uint8_t mult = glcd.font.mult;

    CLR(ILI9341_CS);

    ili9341SetWindow(x0, y0, mult * w, mult * h);

    for (uint16_t i = 0; i < w; i++) {
        for (uint8_t mx = 0; mx < mult; mx++) {
            for (uint16_t j = 0; j < h + 7 / 8; j++) {
                uint8_t data = img->data[w * j + i];
                for (uint8_t bit = 0; bit < 8; bit++) {
                    if (8 * j + bit < h) {
                        if (data & 0x01) {
                            for (uint8_t my = 0; my < mult; my++) {
                                ili9341SendSPI(colorH);
                                ili9341SendSPI(colorL);
                            }
                        } else {
                            for (uint8_t my = 0; my < mult; my++) {
                                ili9341SendSPI(bgColorH);
                                ili9341SendSPI(bgColorL);
                            }
                        }
                        data >>= 1;
                    }
                }
            }
        }
    }

    while (TX_BUSY());
    SET(ILI9341_CS);
}
