WiseLord/ampcontrol-f103/src/settings.h

#ifndef SETTINGS_H
#define SETTINGS_H

#ifdef __cplusplus
extern "C" {
#endif

#include <stdint.h>

#include "action.h"

#define GENERATE_PARAM_RC(CMD)  PARAM_RC_ ## CMD,

typedef uint8_t Param;
enum {
    PARAM_NULL = 0,

    //----------------------------------------------------------------

    PARAM_AUDIO_BEGIN,

    PARAM_AUDIO_IC = PARAM_AUDIO_BEGIN,
    PARAM_AUDIO_INPUT,
    PARAM_AUDIO_SHOWDB,
    PARAM_AUDIO_MODE,
    PARAM_AUDIO_FLAGS,
    PARAM_AUDIO_IN_CFG,

    PARAM_AUDIO_IN0,
    PARAM_AUDIO_IN1,
    PARAM_AUDIO_IN2,
    PARAM_AUDIO_IN3,
    PARAM_AUDIO_IN4,
    PARAM_AUDIO_IN5,
    PARAM_AUDIO_IN6,
    PARAM_AUDIO_IN7,
    PARAM_AUDIO_IN_LAST = PARAM_AUDIO_IN7,

    PARAM_AUDIO_GAIN0,
    PARAM_AUDIO_GAIN1,
    PARAM_AUDIO_GAIN2,
    PARAM_AUDIO_GAIN3,
    PARAM_AUDIO_GAIN4,
    PARAM_AUDIO_GAIN5,
    PARAM_AUDIO_GAIN6,
    PARAM_AUDIO_GAIN7,
    PARAM_AUDIO_GAIN_LAST = PARAM_AUDIO_GAIN7,

    PARAM_AUDIO_VOLUME,
    PARAM_AUDIO_BASS,
    PARAM_AUDIO_MIDDLE,
    PARAM_AUDIO_TREBLE,
    PARAM_AUDIO_BALANCE,
    PARAM_AUDIO_FRONTREAR,
    PARAM_AUDIO_CENTER,
    PARAM_AUDIO_SUBWOOFER,
    PARAM_AUDIO_PREAMP,
    PARAM_AUDIO_LOUDNESS,

    PARAM_AUDIO_BASS_FREQ,
    PARAM_AUDIO_BASS_QUAL,
    PARAM_AUDIO_MIDDLE_FREQ,
    PARAM_AUDIO_MIDDLE_QUAL,
    PARAM_AUDIO_TREBLE_FREQ,
    PARAM_AUDIO_SUB_CUT_FREQ,
    PARAM_AUDIO_LOUD_PEAK_FREQ,

    PARAM_AUDIO_END,

    //----------------------------------------------------------------

    PARAM_TUNER_BEGIN = PARAM_AUDIO_END,

    PARAM_TUNER_IC = PARAM_TUNER_BEGIN,
    PARAM_TUNER_BAND,
    PARAM_TUNER_STEP,
    PARAM_TUNER_DEEMPH,

    PARAM_TUNER_VOLUME,
    PARAM_TUNER_FREQ,
    PARAM_TUNER_FLAGS,

    PARAM_TUNER_FAV_0,
    PARAM_TUNER_FAV_1,
    PARAM_TUNER_FAV_2,
    PARAM_TUNER_FAV_3,
    PARAM_TUNER_FAV_4,
    PARAM_TUNER_FAV_5,
    PARAM_TUNER_FAV_6,
    PARAM_TUNER_FAV_7,
    PARAM_TUNER_FAV_8,
    PARAM_TUNER_FAV_9,

    PARAM_TUNER_END,

    //----------------------------------------------------------------

    PARAM_DISPLAY_BEGIN = PARAM_TUNER_END,

    PARAM_DISPLAY_BR_STBY = PARAM_DISPLAY_BEGIN,
    PARAM_DISPLAY_BR_WORK,
    PARAM_DISPLAY_ROTATE,
    PARAM_DISPLAY_DEF,
    PARAM_DISPLAY_PALETTE,
    PARAM_DISPLAY_SCRSAVER,

    PARAM_SPECTRUM_MODE,
    PARAM_SPECTRUM_PEAKS,
    PARAM_SPECTRUM_GRAD,

    PARAM_ALARM_HOUR,
    PARAM_ALARM_MINUTE,
    PARAM_ALARM_DAYS,

    PARAM_SYSTEM_LANG,
    PARAM_SYSTEM_ENC_RES,
    PARAM_SYSTEM_SIL_TIM,
    PARAM_SYSTEM_RTC_CORR,
    PARAM_SYSTEM_STBY_LOW,
    PARAM_SYSTEM_MUTE_LOW,

    PARAM_I2C_EXT_IN_STAT,
    PARAM_I2C_EXT_GPIO,

    FOREACH_CMD(GENERATE_PARAM_RC)

    PARAM_END
};

void settingsInit(void);

int16_t settingsRead(Param param, int16_t defValue);
void settingsStore(Param param, int16_t value);

#ifdef __cplusplus
}
#endif

#endif // SETTINGS_H
